ngrigoriev/dactyl-manuform-5x7_2_6/pics/kbpic_23.jpg

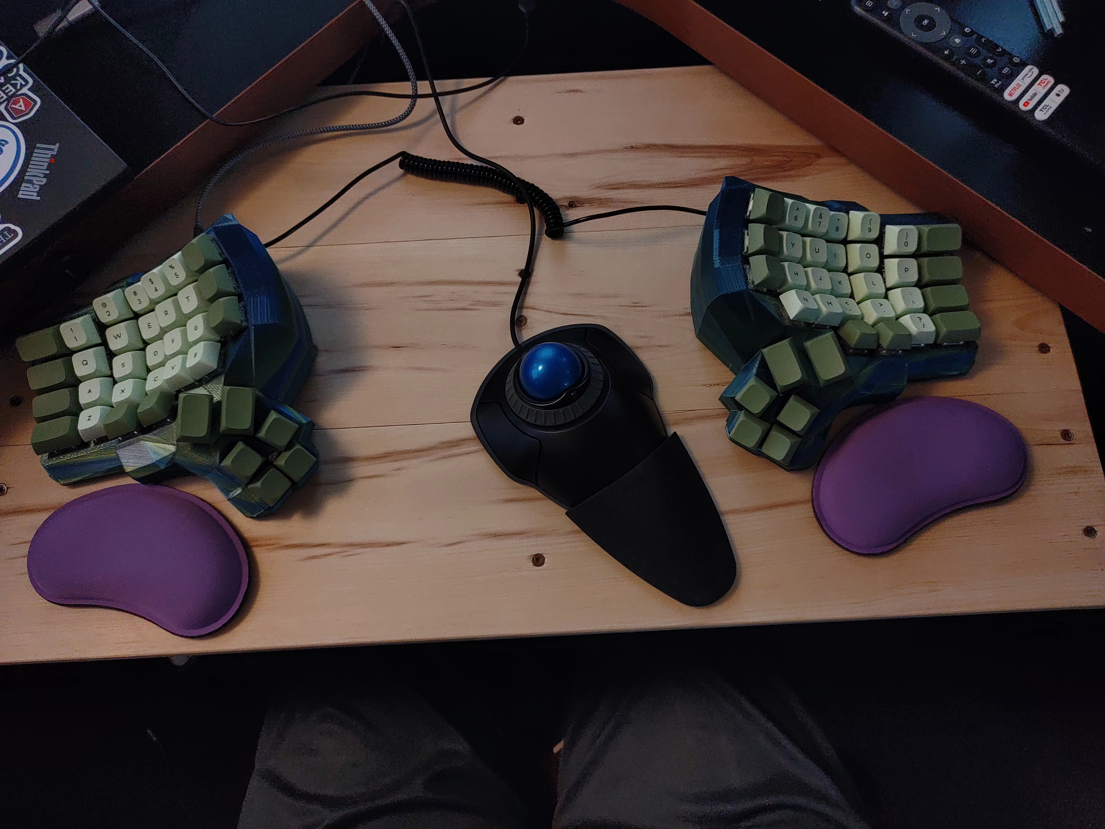
pics/kbpic_23.jpg
